ingeninge/Wasserhahn/images/20190403_161359.jpg

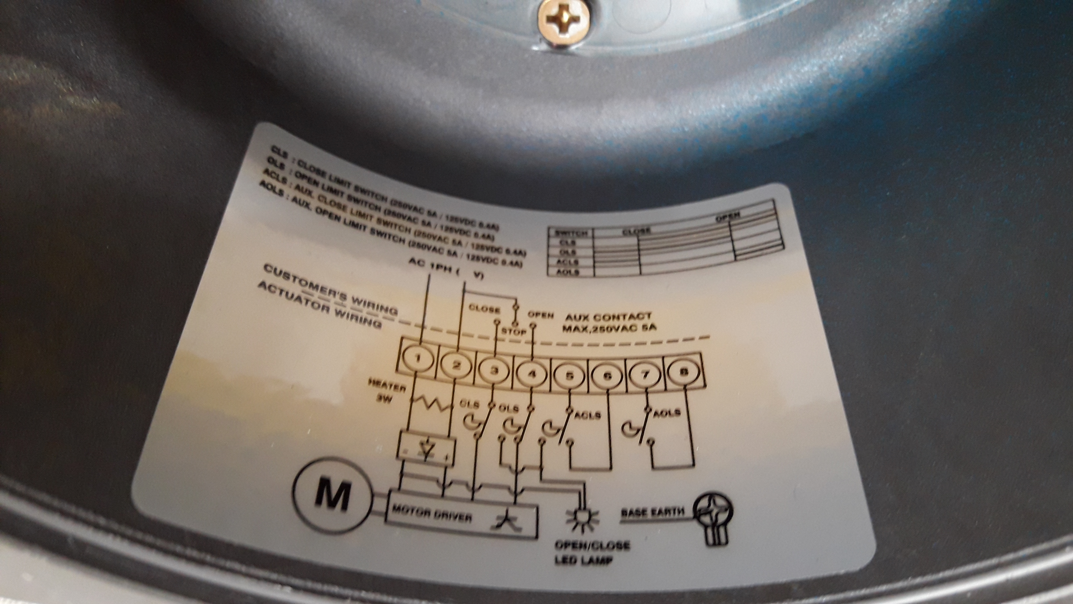
images/20190403_161359.jpg
